corrubimbo/S.O.N.A.R.I.S/hardware/SpeakerSystem.kicad_sch

## KiCad design hardware/SpeakerSystem.kicad_sch (2026-07-10)

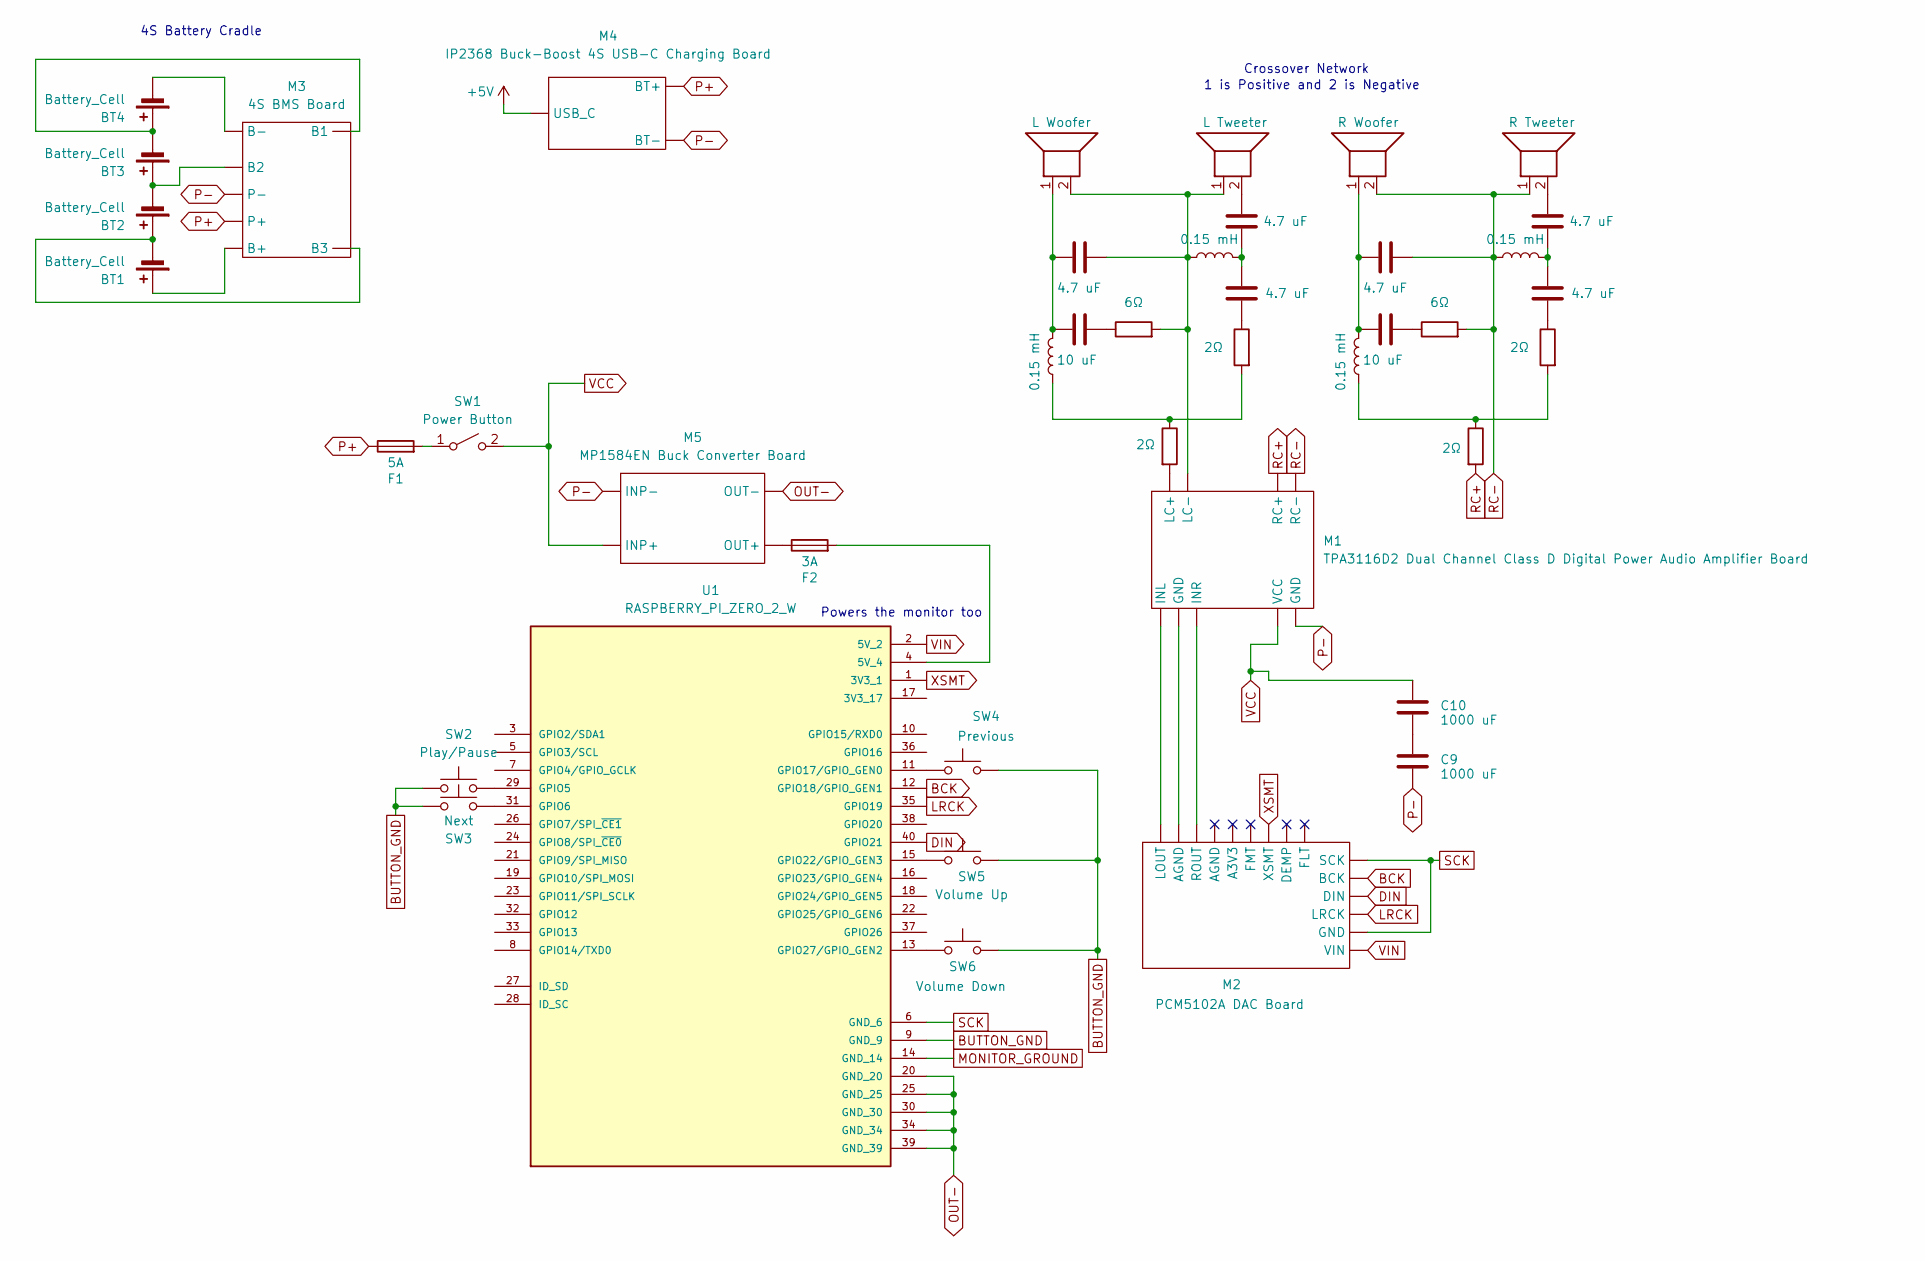
[picture p6: schematic SpeakerSystem.kicad_sch]

Parts:
BT1, BT2, BT3, BT4: Battery_Cell
C1, C2, C4, C5, C7, C8: 4.7 uF
C3, C6: 10 uF
C9, C10: 1000 uF
F1: 5A
F2: 3A
L1, L2, L3, L4: 0.15 mH
LS1: L Tweeter
LS2: L Woofer
LS3: R Woofer
LS4: R Tweeter
M1: TPA3116D2 Dual Channel Class D Digital Power Audi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
M2: PCM5102A DAC Board
M3: 4S BMS Board
M4: IP2368 Buck-Boost 4S USB-C Charging Board
M5: MP1584EN Buck Converter Board
R1, R2, R5, R6: 2Ω
R3, R4: 6Ω
SW1: Power Button
SW2: Play/Pause
SW3: Next
SW4: Previous
SW5: Volume Up
SW6: Volume Down
U1: RASPBERRY_PI_ZERO_2_W; MODULE_RASPBERRY_PI_ZERO_2_W; PARTREV April 2024

Connections:
+5V: M4.
BCK: M2., U1.12 (GPIO18/GPIO_GEN1)
BUTTON_GND: SW2.1, SW3.1, SW4.2, SW5.2, SW6.2, U1.9 (GND_9)
DIN: M2., U1.40 (GPIO21)
LRCK: M2., U1.35 (GPIO19)
MONITOR_GROUND: U1.14 (GND_14)
unnamed: BT1.1 (+), M3.
unnamed: BT1.2 (-), BT2.1 (+), M3.
unnamed: BT2.2 (-), BT3.1 (+), M3.
unnamed: BT3.2 (-), BT4.1 (+), M3.
unnamed: BT4.2 (-), M3.
unnamed: C1.1, C2.2, L1.1
unnamed: C1.2, R2.1
unnamed: C2.1, LS1.2
unnamed: C3.1, R3.1
unnamed: C3.2, C4.2, L2.1, LS2.1
unnamed: C4.1, L1.2, LS1.1, LS2.2, M1., R3.2
unnamed: C5.2, C6.2, L3.1, LS3.1
unnamed: C6.1, R4.1
unnamed: C7.1, LS4.2
unnamed: C7.2, C8.1, L4.1
unnamed: C8.2, R6.1
unnamed: C9.1, C10.2
unnamed: F1.2, SW1.1 (A)
unnamed: F2.1, M5.
unnamed: F2.2, U1.4 (5V_4)
unnamed: L2.2, R1.1, R2.2
unnamed: L3.2, R5.1, R6.2
unnamed: M1., M2., R1.2
unnamed: SW2.2, U1.29 (GPIO5)
unnamed: SW3.2, U1.31 (GPIO6)
unnamed: SW4.1, U1.11 (GPIO17/GPIO_GEN0)
unnamed: SW5.1, U1.15 (GPIO22/GPIO_GEN3)
unnamed: SW6.1, U1.13 (GPIO27/GPIO_GEN2)
OUT-: M5., U1.20 (GND_20), U1.25 (GND_25), U1.30 (GND_30), U1.34 (GND_34), U1.39 (GND_39)
P+: F1.1, M3., M4.
P-: C9.2, M1., M3., M4., M5.
RC+: M1., R5.2
RC-: C5.1, L4.2, LS3.2, LS4.1, M1., R4.2
SCK: M2., U1.6 (GND_6)
VCC: C10.1, M1., M5., SW1.2 (B)
VIN: M2., U1.2 (5V_2)
XSMT: M2., U1.1 (3V3_1)

Notes on the sheet:
Crossover Network
4S Battery Cradle
Powers the monitor too
1 is Positive and 2 is Negative
